makermoekoe/Picoclick-C3/docs/ext_board_pir_bot.png

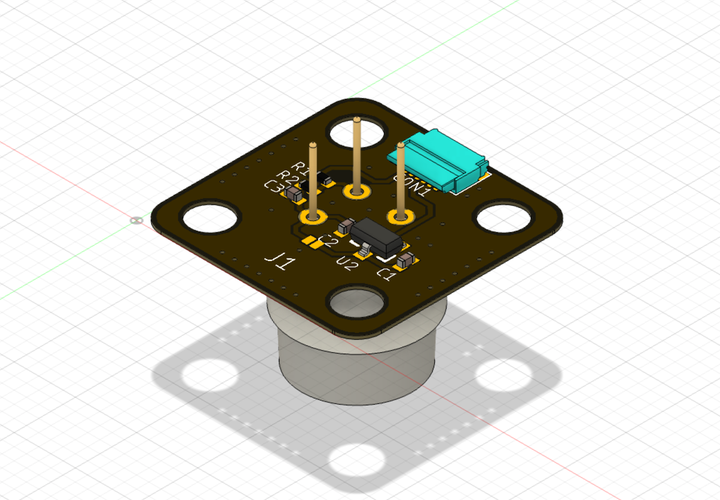
docs/ext_board_pir_bot.png
