makermoekoe/Picoclick-C3/docs/ext_board_pir_top.png

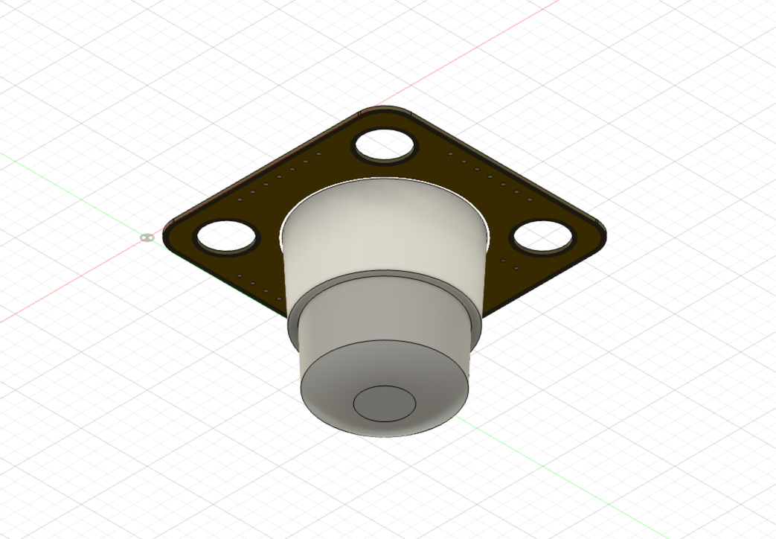
docs/ext_board_pir_top.png
