makermoekoe/Picoclick-C3/docs/pc3_button.jpg

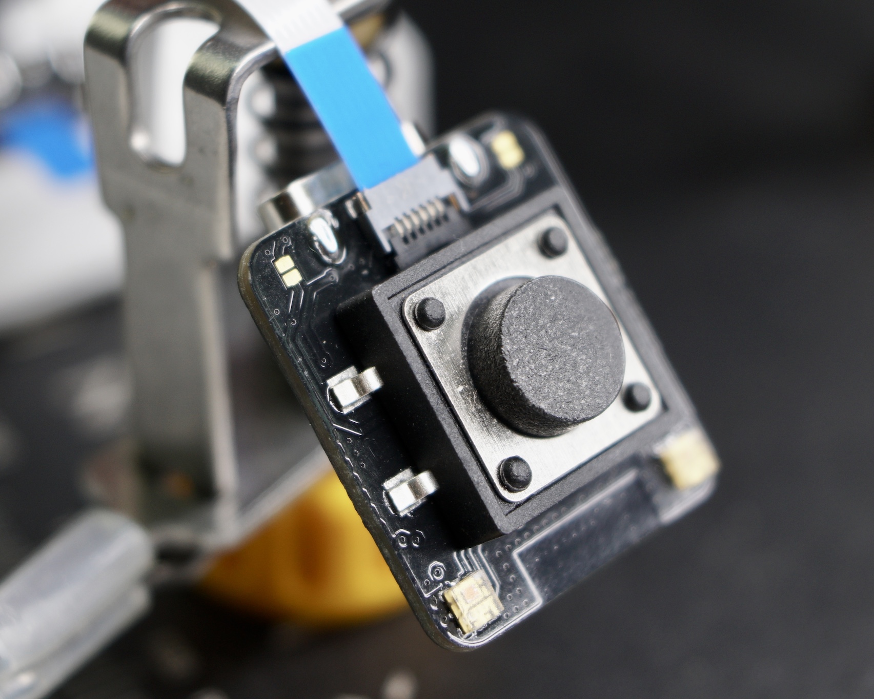
docs/pc3_button.jpg
