makermoekoe/Picoclick-C3/docs/pc3_case1_model.jpg

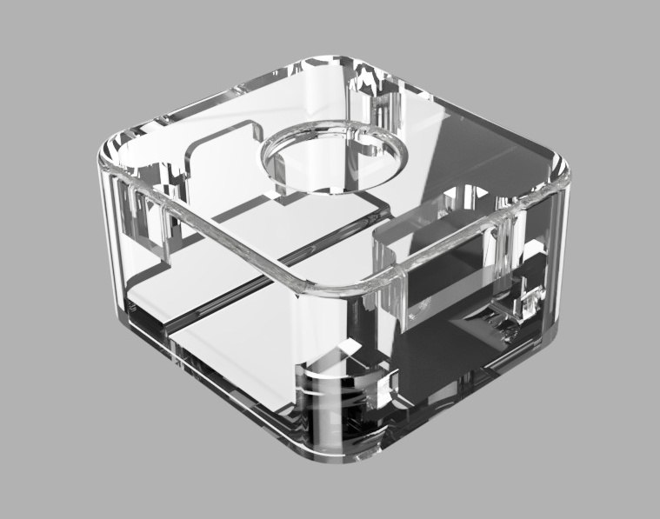
docs/pc3_case1_model.jpg
