makermoekoe/Picoclick-C3/case/Picoclick_C3/pc3_ext_motion_v2.stl

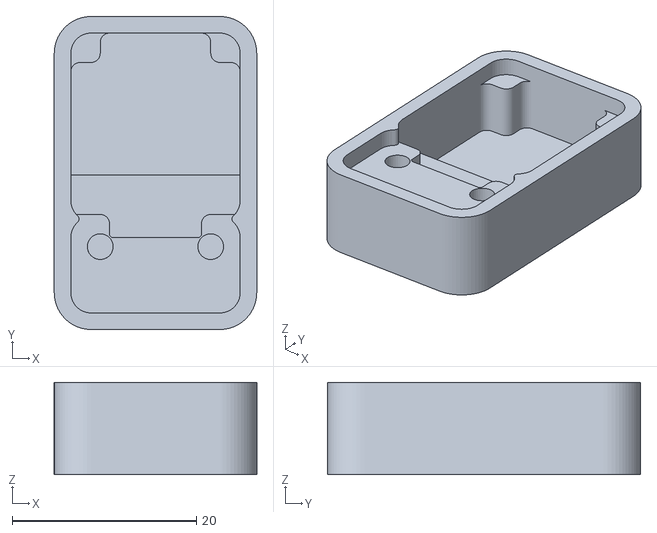
[picture p37: CAD file, 2022-12-02]
case/Picoclick_C3/pc3_ext_motion_v2.stl
22.0 x 34.0 x 10.00
