makermoekoe/Picoclick-C3/case/Picoclick_C3/pc3_pogopin_adapter_bat_v1.stl

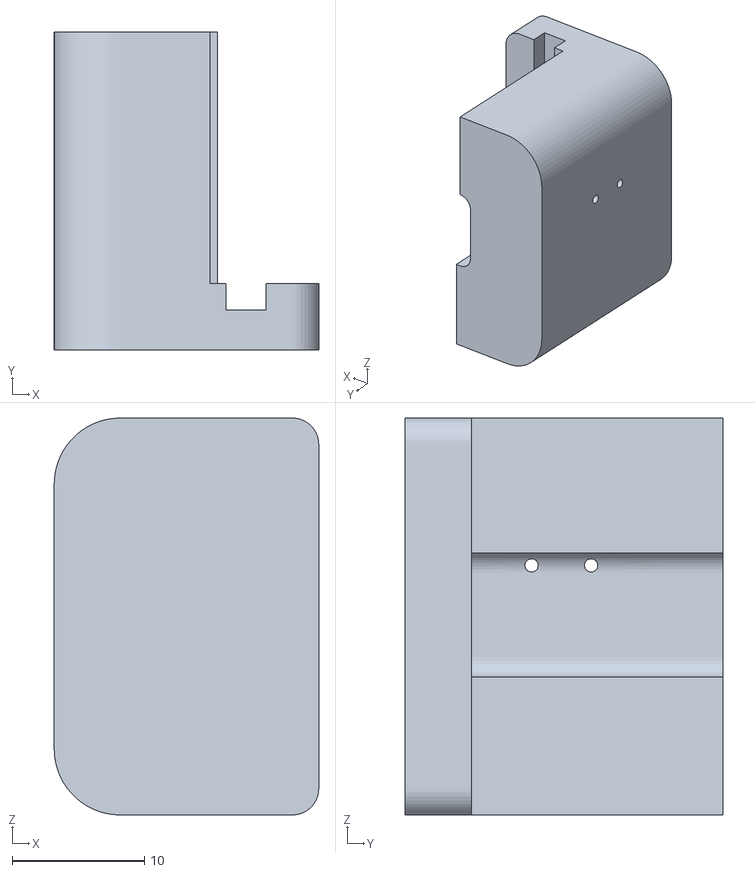
[picture p38: CAD file, 2022-12-02]
case/Picoclick_C3/pc3_pogopin_adapter_bat_v1.stl
20.0 x 24.0 x 30.0
